leaflabs/maple/maple-r1/maple-r1-bottom.png

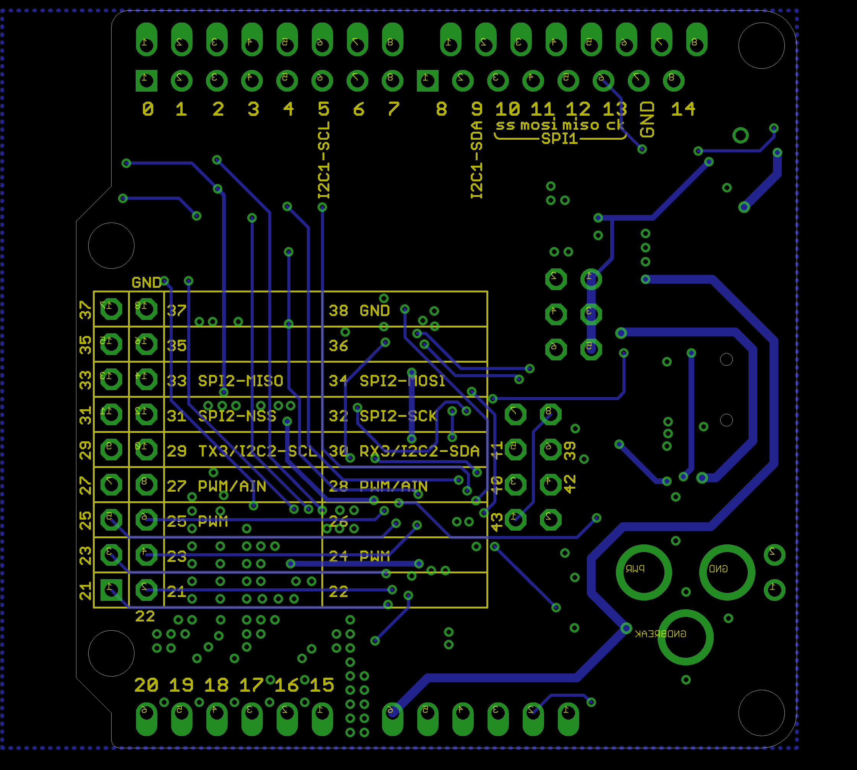
maple-r1/maple-r1-bottom.png
