leaflabs/maple/maple-r1/maple-r1-top.png

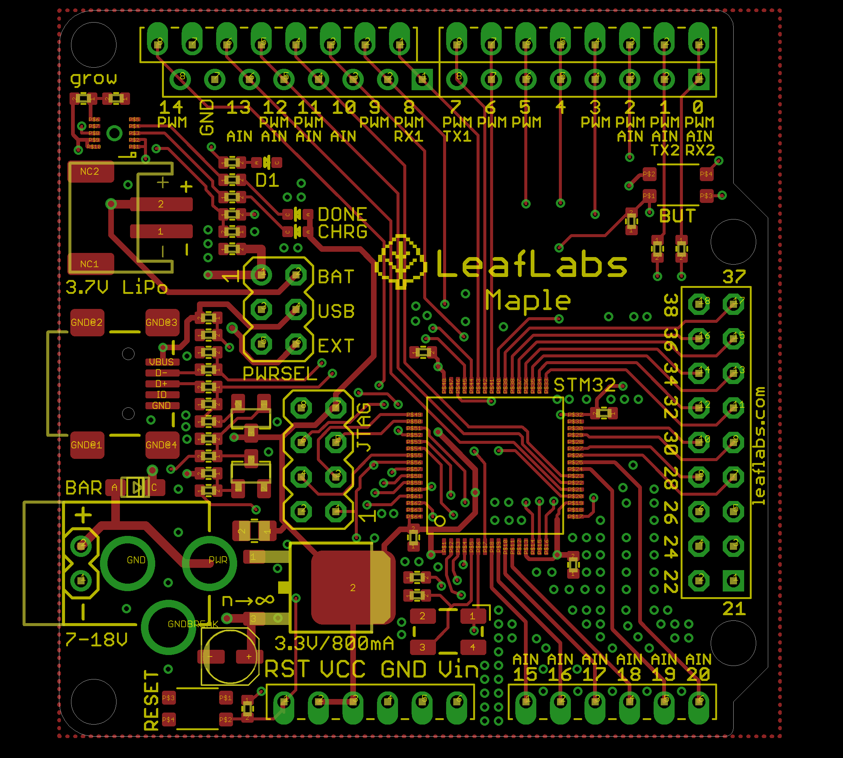
maple-r1/maple-r1-top.png
