leaflabs/maple/maple-r3/maple-r3-bottom.png

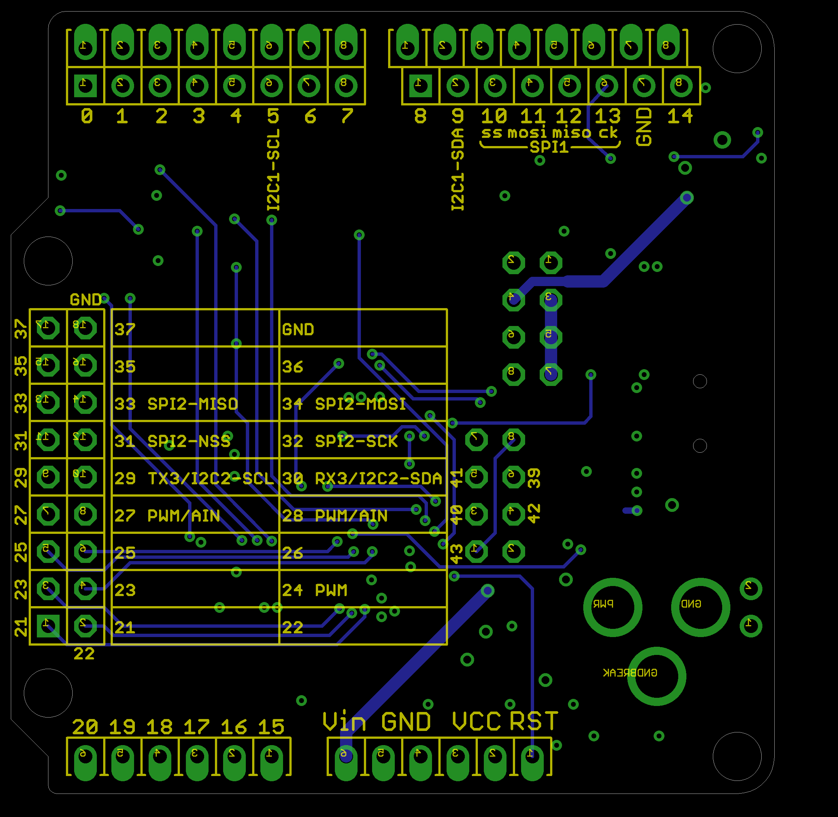
maple-r3/maple-r3-bottom.png
