leaflabs/maple/test-procedures/unmelted-solder.jpg

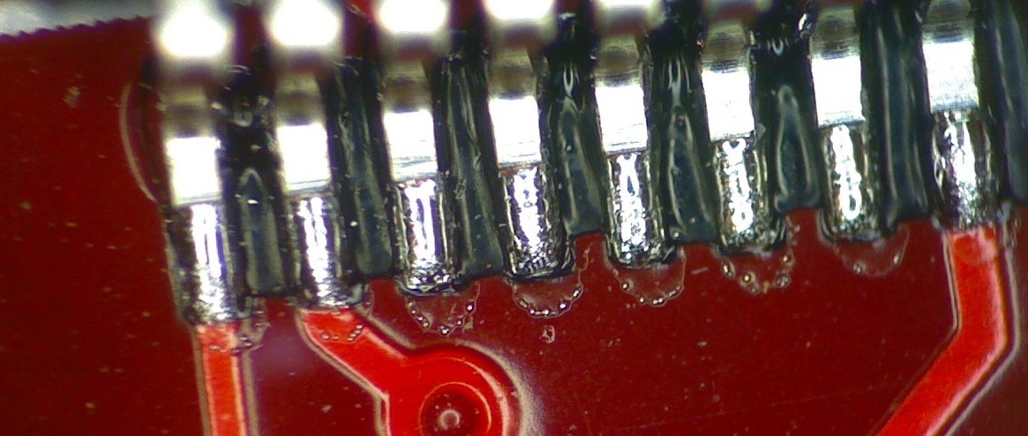
test-procedures/unmelted-solder.jpg
