leaflabs/maple/test-procedures/overheated-reset-button.jpg

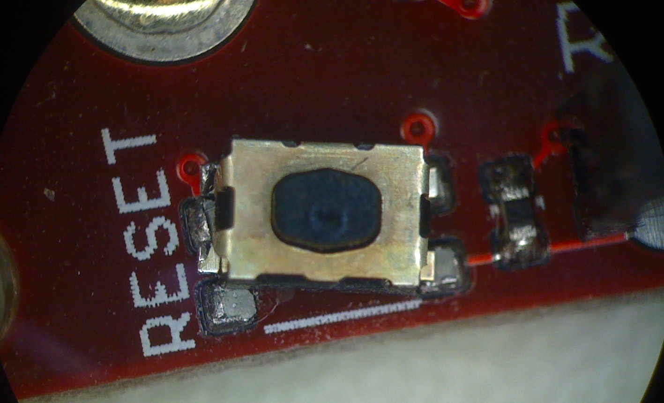
test-procedures/overheated-reset-button.jpg
