leaflabs/maple/test-procedures/shield-bottom.jpg

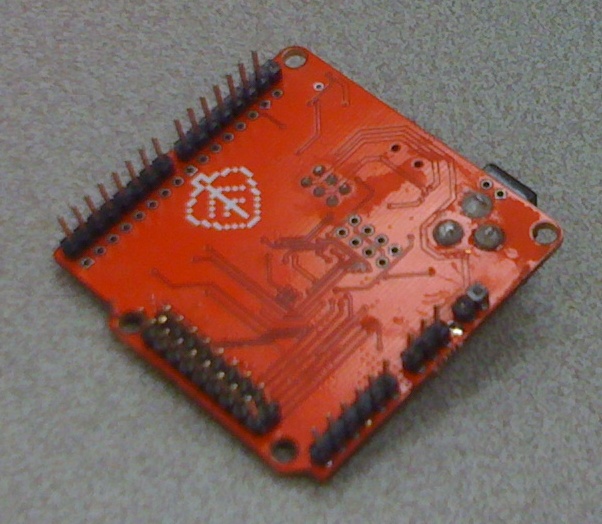
test-procedures/shield-bottom.jpg
