leaflabs/maple/test-procedures/test-shield-attached.jpg

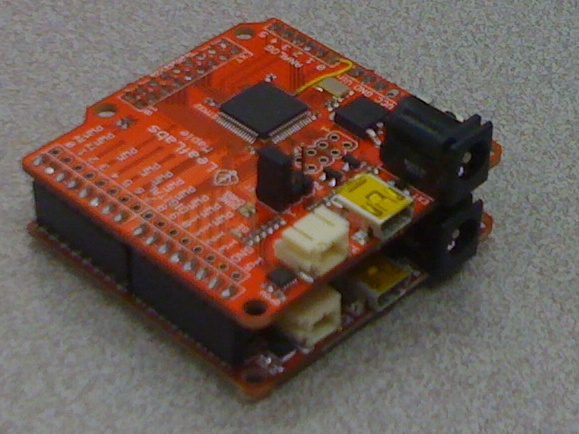
test-procedures/test-shield-attached.jpg
